loublock/Adam-Soundbox/CAD/Renderings/2.png

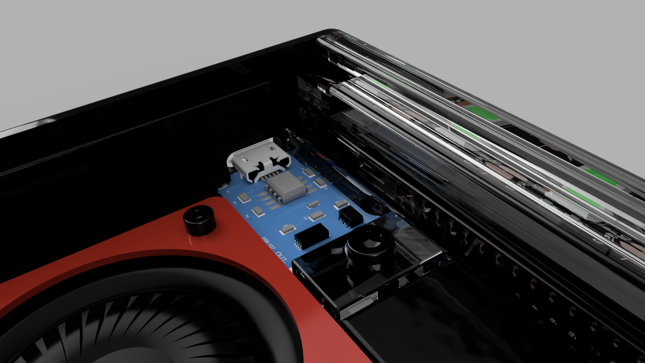
CAD/Renderings/2.png
