loublock/Adam-Soundbox/CAD/Renderings/4.png

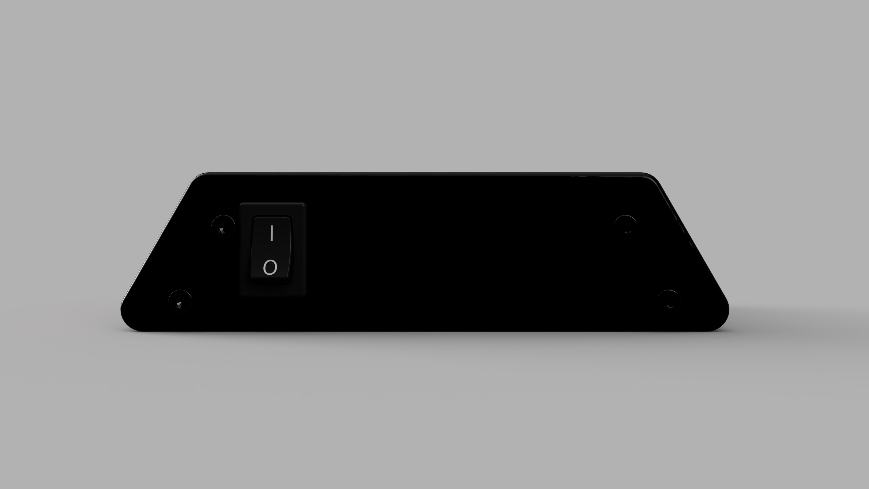
CAD/Renderings/4.png
