loublock/Adam-Soundbox/CAD/Renderings/6.png

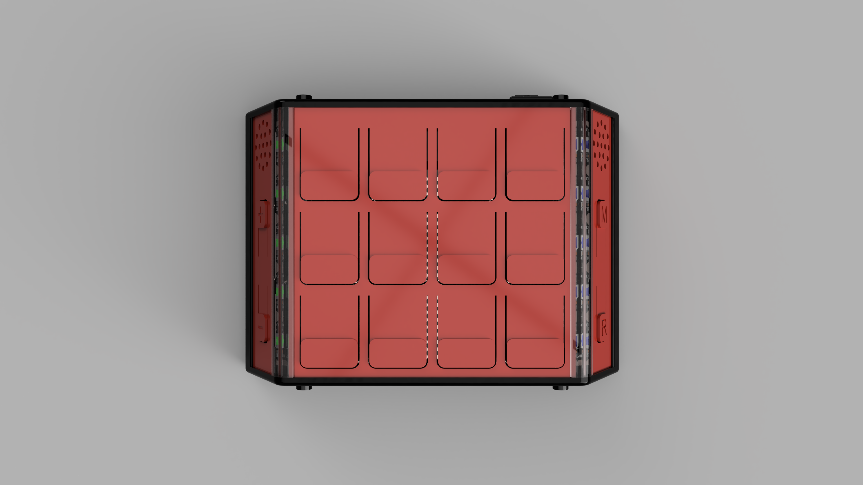
CAD/Renderings/6.png
