loublock/Adam-Soundbox/CAD/Renderings/7.png

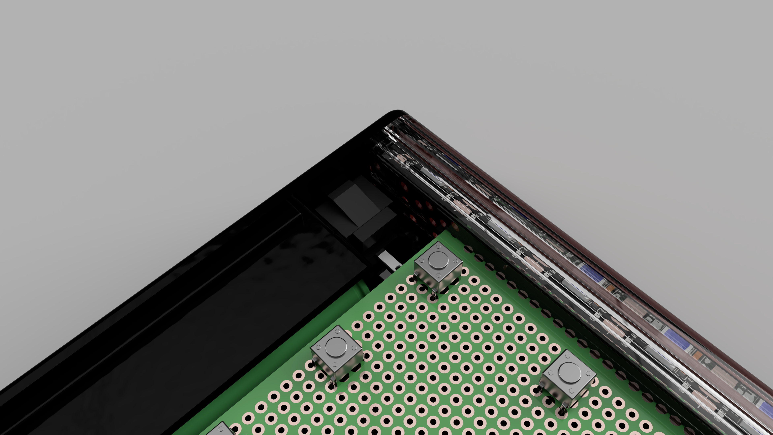
CAD/Renderings/7.png
