loublock/Adam-Soundbox/CAD/Renderings/8.png

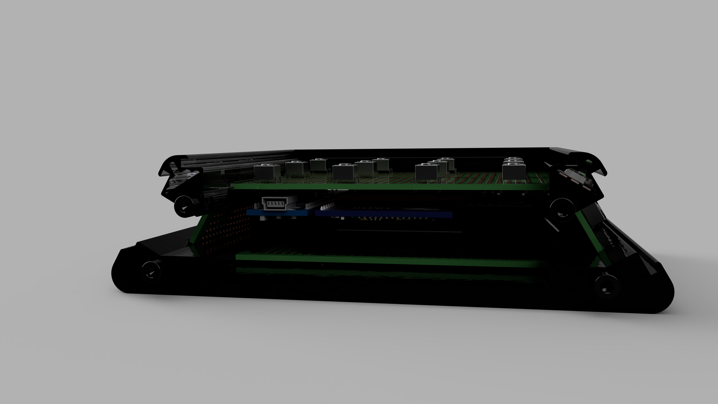
CAD/Renderings/8.png
